mdeweerd/openfixture/3dmodels/R50-2S-P50-B1.step

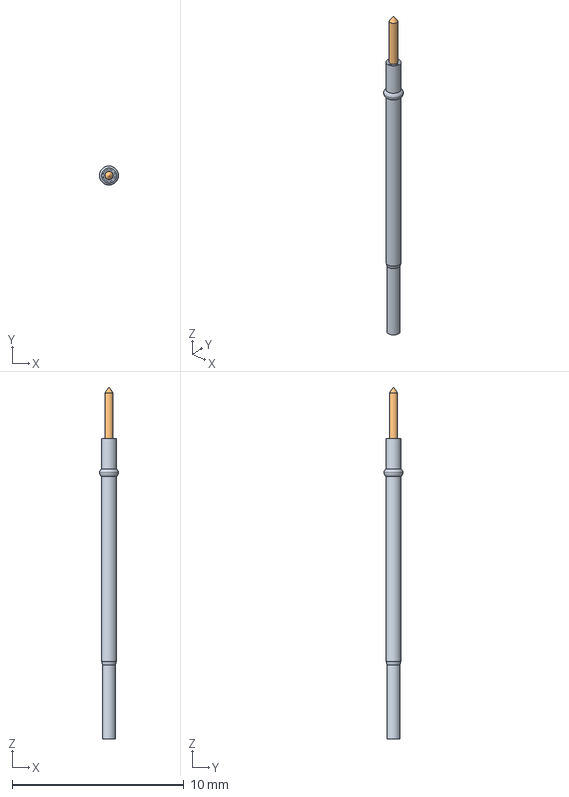
[picture p15: CAD file, 2024-01-05]
3dmodels/R50-2S-P50-B1.step
1.11 x 1.11 x 20.5 mm
