mdeweerd/openfixture/3dmodels/R100-3T-P100-A2.step

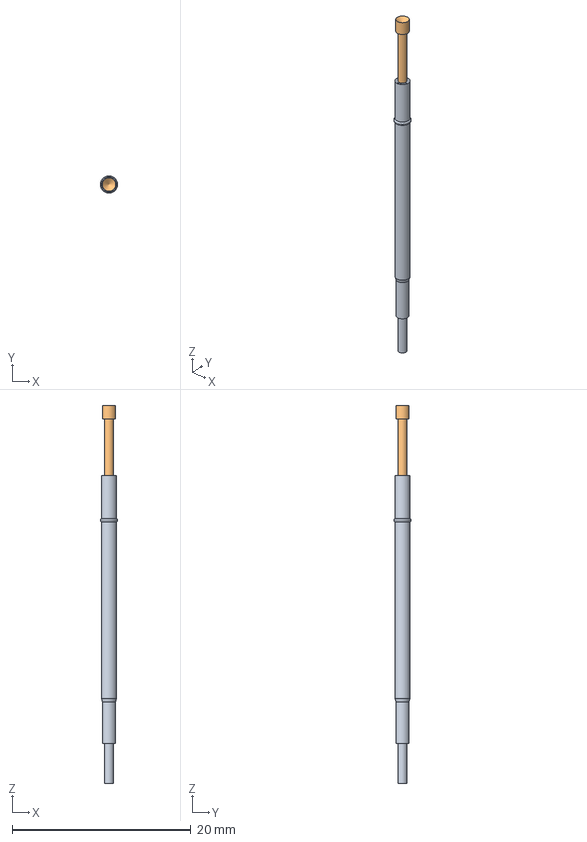
[picture p16: CAD file, 2024-01-05]
3dmodels/R100-3T-P100-A2.step
1.93 x 1.93 x 42.4 mm
