mdeweerd/openfixture/3dmodels/R50-1S-P50-E2.step

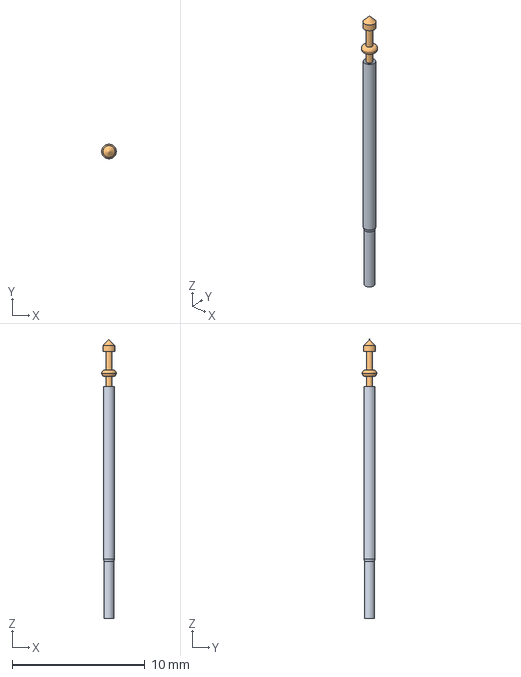
[picture p18: CAD file, 2024-01-05]
3dmodels/R50-1S-P50-E2.step
1.11 x 1.11 x 21.0 mm
