mdeweerd/openfixture/3dmodels/R100-3T-P100-B1.step

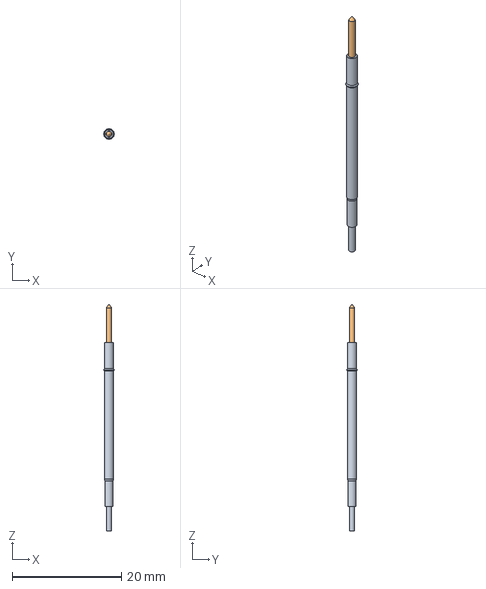
[picture p19: CAD file, 2024-01-05]
3dmodels/R100-3T-P100-B1.step
1.93 x 1.93 x 41.6 mm
