mdeweerd/openfixture/3dmodels/P100-E2.step

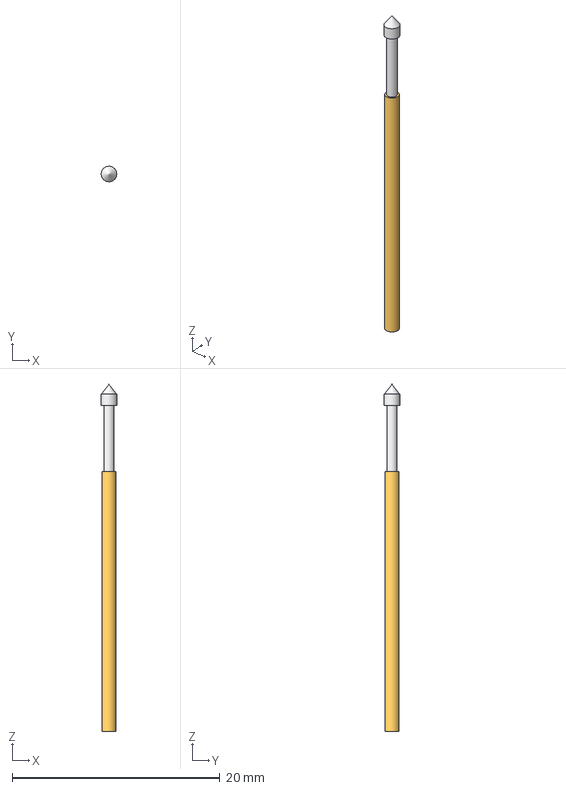
[picture p20: CAD file, 2024-01-05]
3dmodels/P100-E2.step
1.50 x 1.50 x 33.4 mm
