mdeweerd/openfixture/3dmodels/R100-3T-P100-E2.step

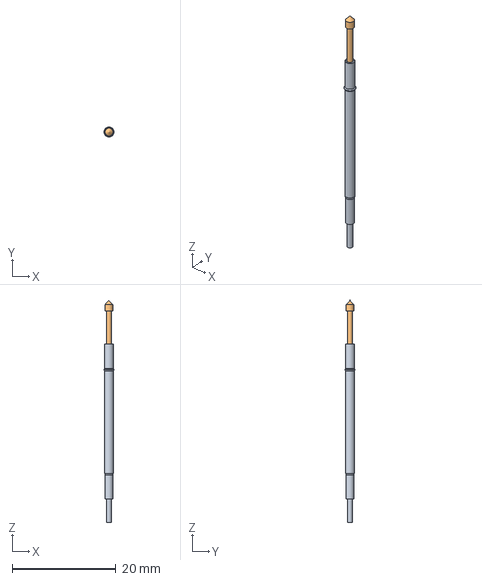
[picture p21: CAD file, 2024-01-05]
3dmodels/R100-3T-P100-E2.step
1.93 x 1.93 x 42.9 mm
