mdeweerd/openfixture/3dmodels/R100-4VW-P100-B1.step

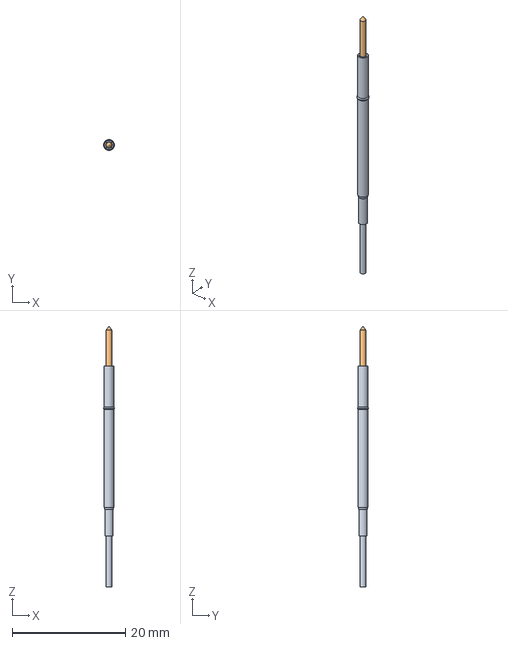
[picture p23: CAD file, 2024-01-05]
3dmodels/R100-4VW-P100-B1.step
1.93 x 1.93 x 46.1 mm
