mdeweerd/openfixture/3dmodels/P50-Q1.step

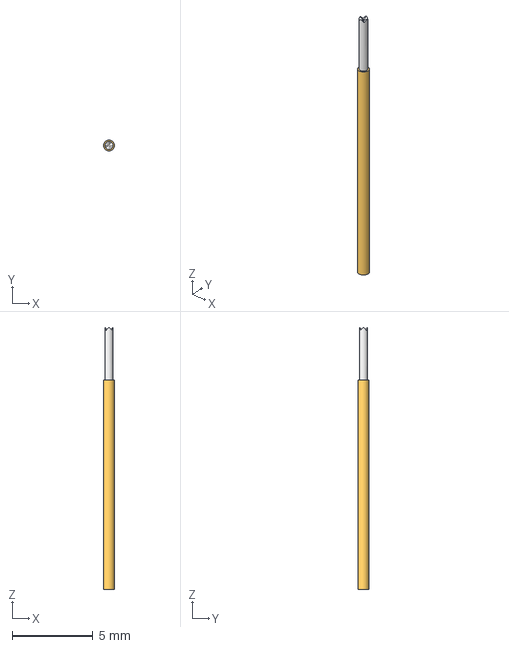
[picture p24: CAD file, 2024-01-05]
3dmodels/P50-Q1.step
0.679 x 0.68 x 16.3 mm
