mdeweerd/openfixture/3dmodels/P058-Q1.step

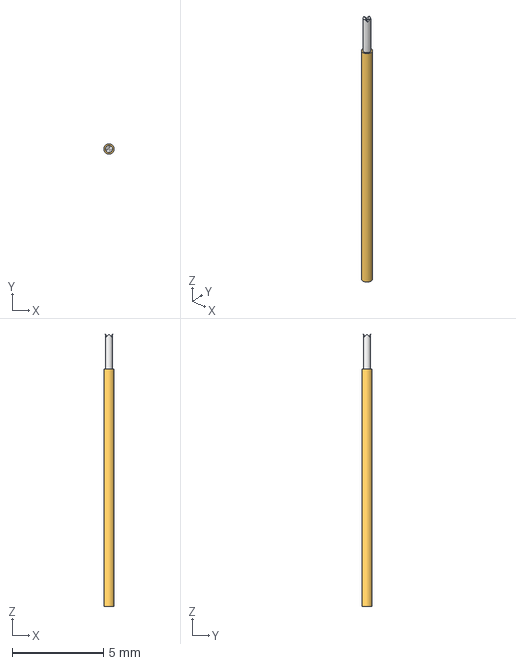
[picture p25: CAD file, 2024-01-05]
3dmodels/P058-Q1.step
0.559 x 0.56 x 14.9 mm
