mdeweerd/openfixture/3dmodels/P75-E2.step

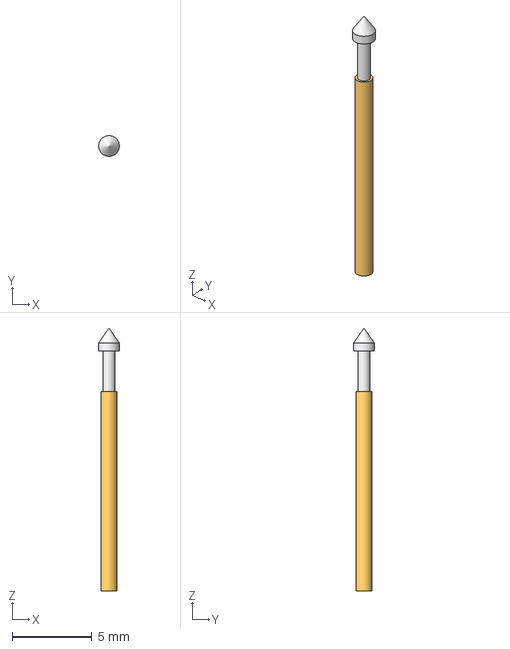
[picture p26: CAD file, 2024-01-05]
3dmodels/P75-E2.step
1.30 x 1.30 x 16.5 mm
