mdeweerd/openfixture/3dmodels/R100-2S-P100-B1.step

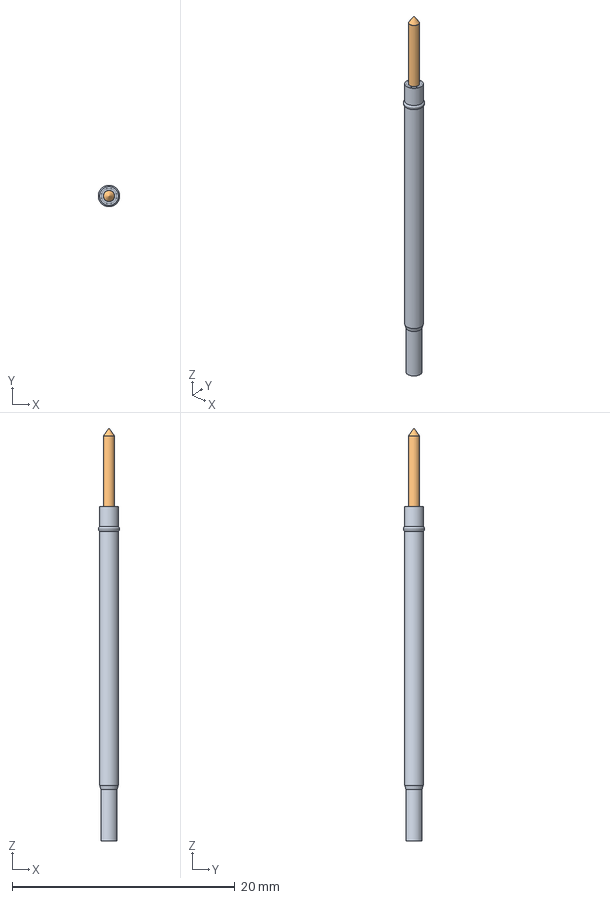
[picture p27: CAD file, 2024-01-05]
3dmodels/R100-2S-P100-B1.step
1.93 x 1.93 x 37.1 mm
