mdeweerd/openfixture/3dmodels/R50-1S-P50-E3.step

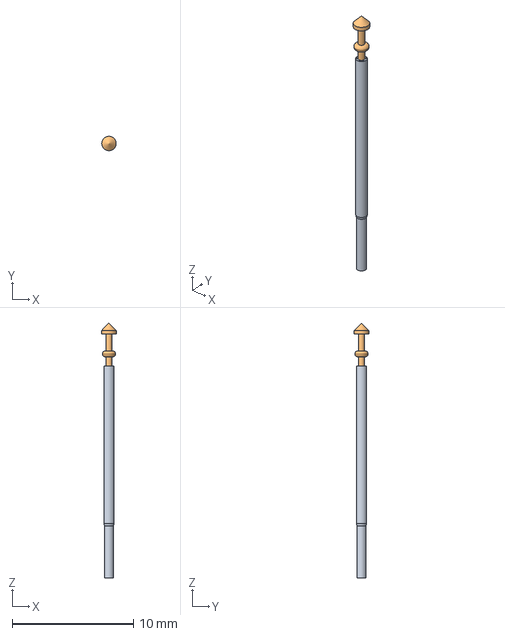
[picture p28: CAD file, 2024-01-05]
3dmodels/R50-1S-P50-E3.step
1.20 x 1.20 x 21.0 mm
