mdeweerd/openfixture/3dmodels/P50-E1.step

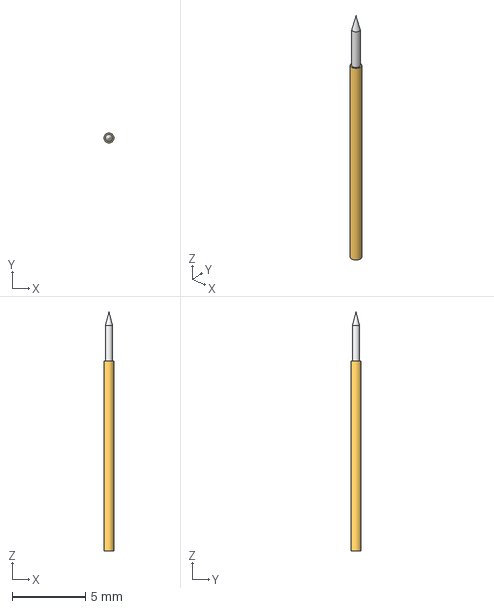
[picture p29: CAD file, 2024-01-05]
3dmodels/P50-E1.step
0.679 x 0.68 x 16.4 mm
