mdeweerd/openfixture/3dmodels/a.step

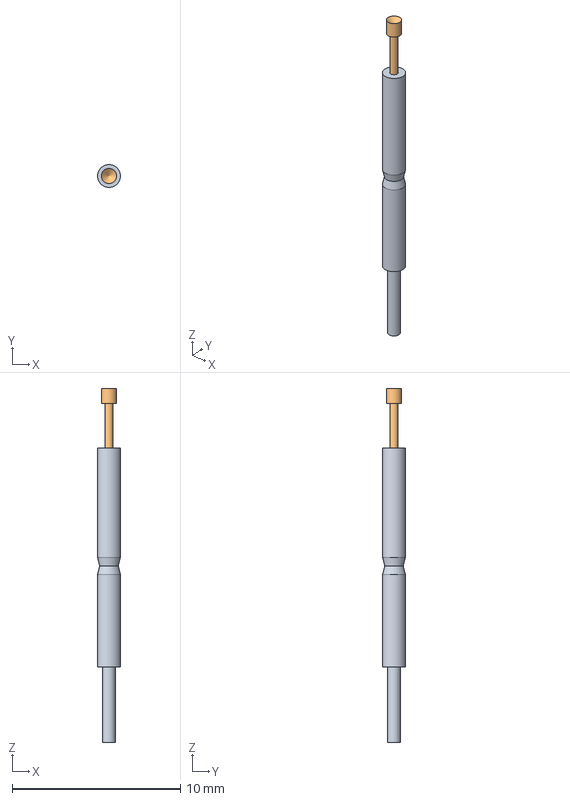
[picture p30: CAD file, 2024-01-05]
3dmodels/a.step
1.36 x 1.36 x 21.1 mm
